cHemingway/babys_first_beats/cad/langair_v12_antivandalswitch.SLDPRT

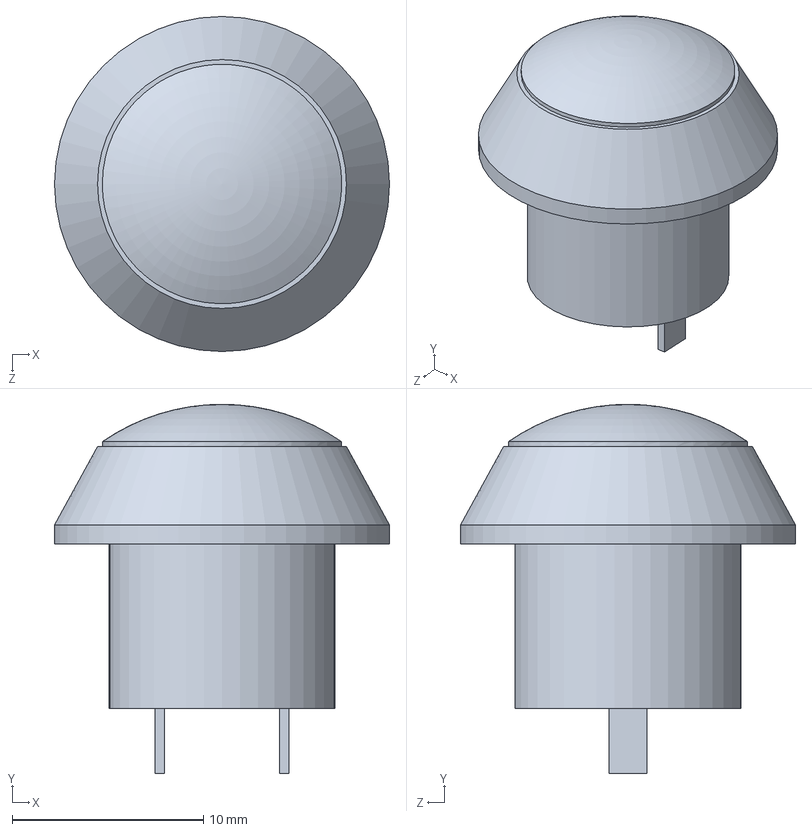
[picture p16: CAD file, 2025-07-09]
cad/langair_v12_antivandalswitch.SLDPRT
17.5 x 19.3 x 17.5 mm
