cHemingway/babys_first_beats/cad/4682 Micro SD Breakout.SLDPRT

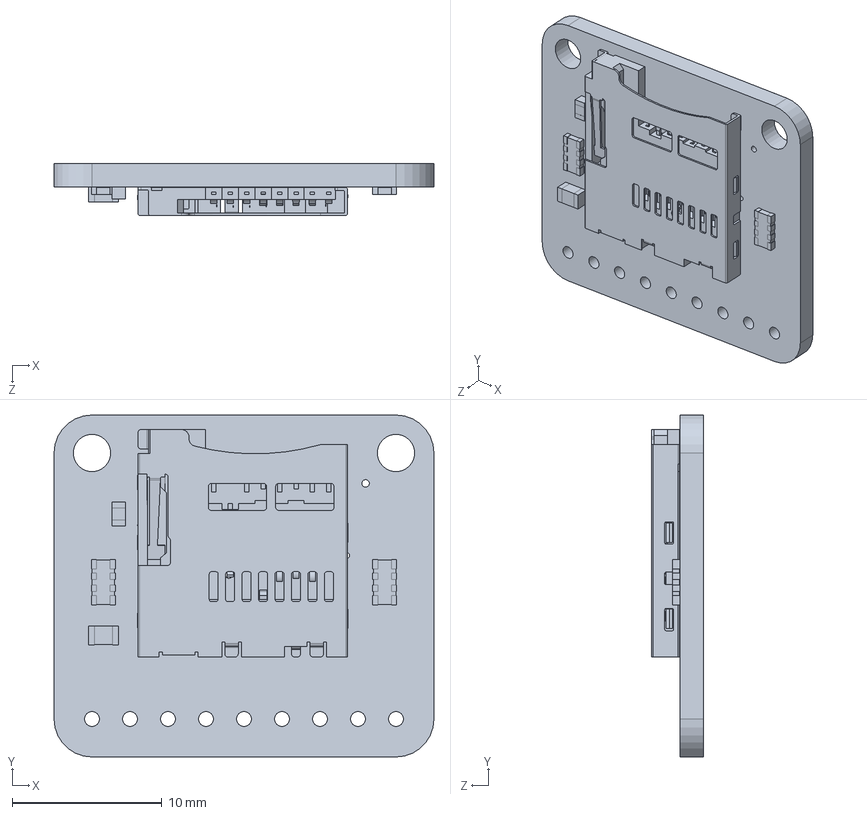
[picture p17: CAD file, 2025-07-09]
cad/4682 Micro SD Breakout.SLDPRT
25.4 x 22.9 x 3.45 mm
