cHemingway/babys_first_beats/cad/Volume Knob.SLDPRT

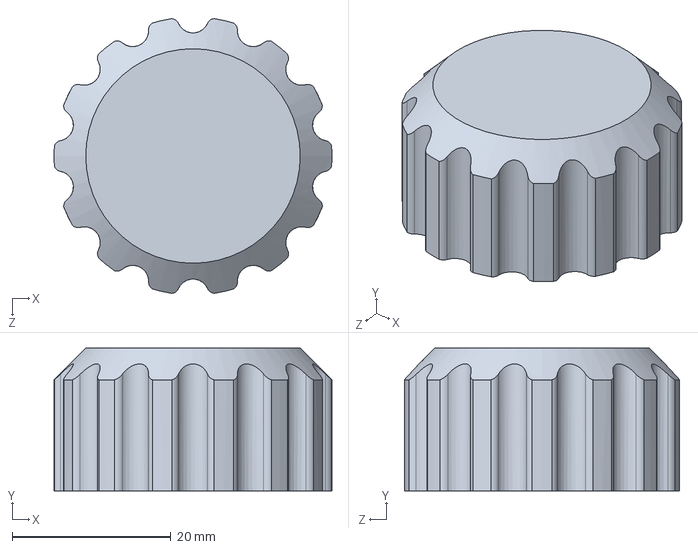
[picture p18: CAD file, 2025-07-09]
cad/Volume Knob.SLDPRT
35.0 x 18.0 x 34.6 mm
