cHemingway/babys_first_beats/cad/SpeakerGrillV1.SLDPRT

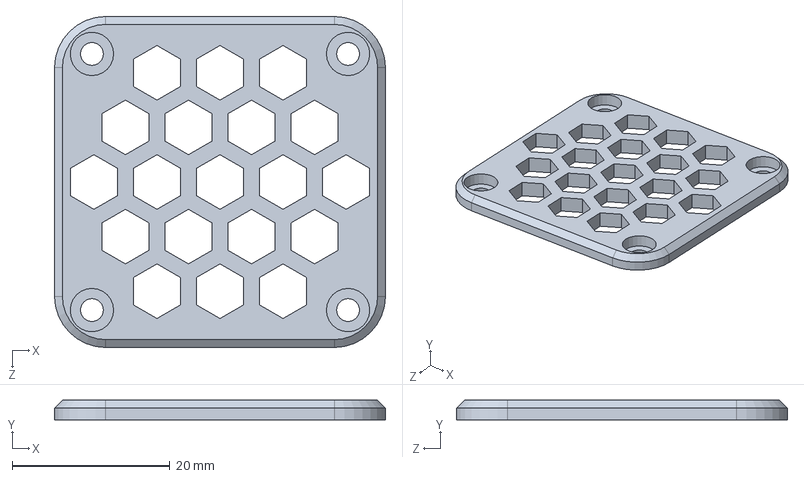
[picture p19: CAD file, 2025-07-09]
cad/SpeakerGrillV1.SLDPRT
42.0 x 2.50 x 42.0 mm
