cHemingway/babys_first_beats/cad/battery_clamp_v1.SLDPRT

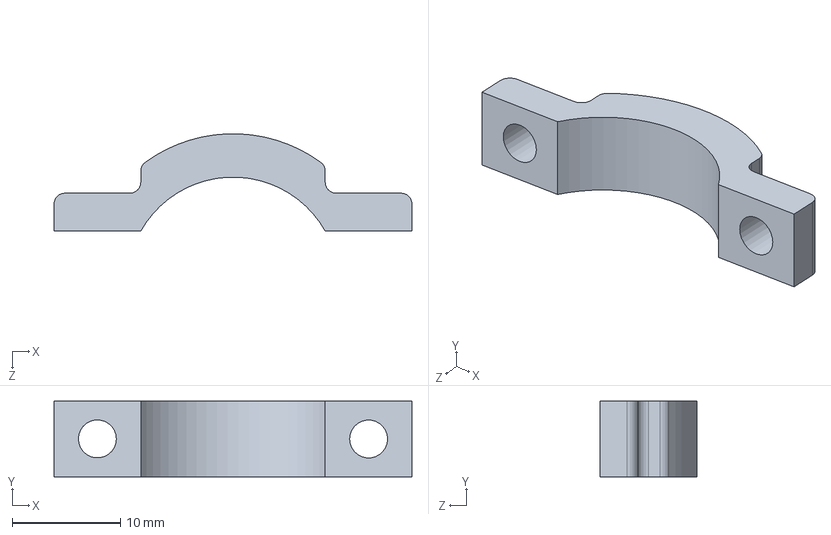
[picture p20: CAD file, 2025-07-09]
cad/battery_clamp_v1.SLDPRT
33.0 x 7.00 x 8.96 mm
