cHemingway/babys_first_beats/cad/case_split_bottom.SLDPRT

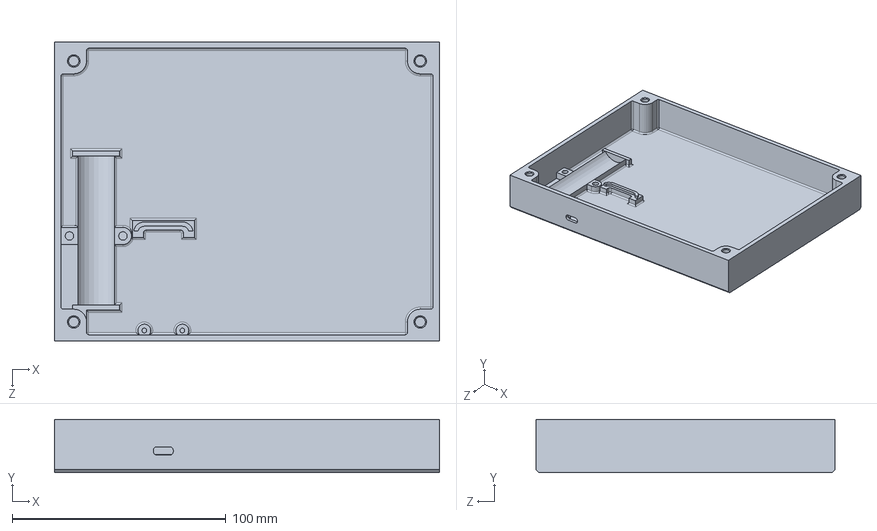
[picture p21: CAD file, 2025-07-09]
cad/case_split_bottom.SLDPRT
180.0 x 25.0 x 140.0 mm
