cHemingway/babys_first_beats/cad/case_profile_extrusion.SLDPRT

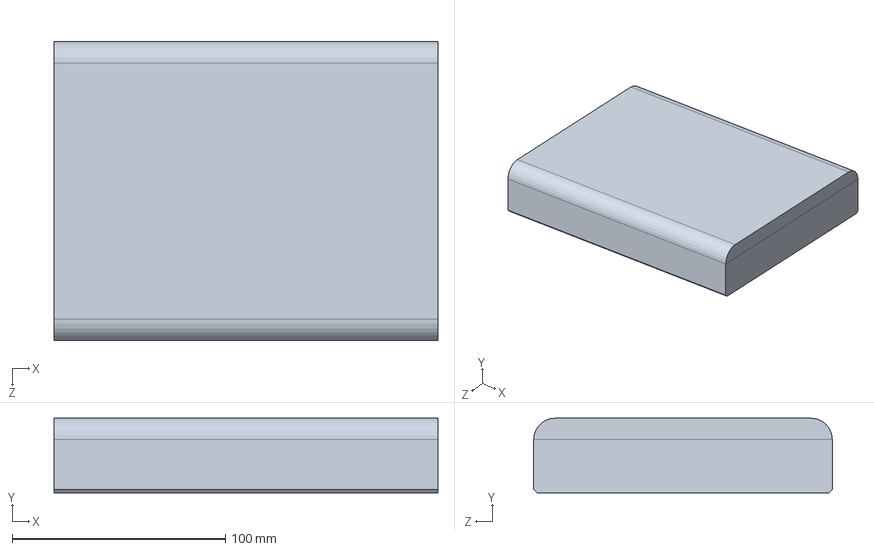
[picture p22: CAD file, 2025-07-09]
cad/case_profile_extrusion.SLDPRT
180.0 x 35.0 x 140.0 mm
