cHemingway/babys_first_beats/cad/arcade_button_small.SLDPRT

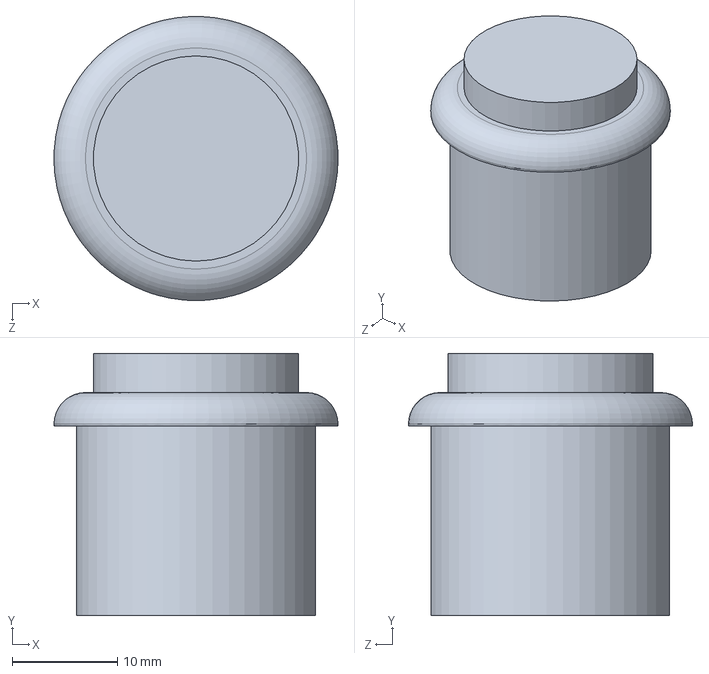
[picture p23: CAD file, 2025-07-09]
cad/arcade_button_small.SLDPRT
27.0 x 24.9 x 27.0 mm
