cHemingway/babys_first_beats/cad/assembly_v1.SLDASM

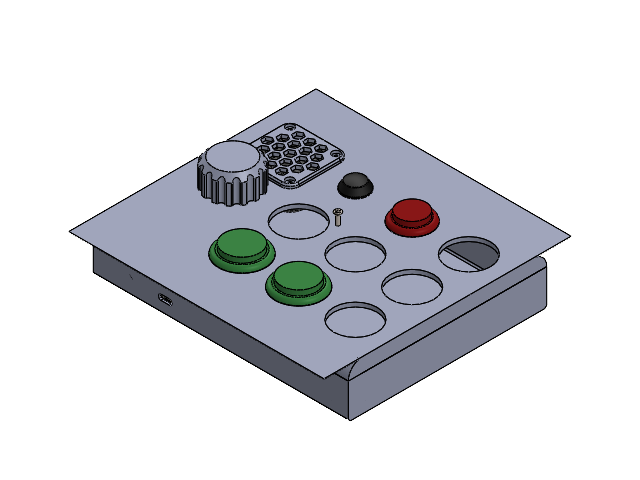
[picture p24: CAD file, 2025-07-09]
cad/assembly_v1.SLDASM
arcade_button_large x 2
arcade_button_small
5768 Feather RP2040 PropMaker
PKCELL_ICR18650_Wired
case_split_bottom
case_split_top_v2
4682 Micro SD Breakout
battery_clamp_v1
1400 Push Button Power Switch
langair_v12_antivandalswitch
P231-FC20BR10K
3968 Speaker 40mm
Hexagon Nut ISO 4032 - M2.5 - W - N x 4
Volume Knob
SpeakerGrillV1
DIN EN ISO 7046-1 - M2.5 x 8 - Z - 8N x 5
DIN 6902-C2.25 x 4
